HadarYisthak/MIPS-Based-MCU-Design/MCU Project/DUT/PLL.vhd

LIBRARY ieee;
USE ieee.std_logic_1164.all;

LIBRARY altera_mf;
USE altera_mf.all;

ENTITY PLL IS
	PORT
	(
		areset		: IN STD_LOGIC  := '0';
		inclk0		: IN STD_LOGIC  := '0';
		c0		: OUT STD_LOGIC ;
		locked		: OUT STD_LOGIC 
	);
END PLL;


ARCHITECTURE SYN OF pll IS

	SIGNAL sub_wire0	: STD_LOGIC ;
	SIGNAL sub_wire1	: STD_LOGIC_VECTOR (5 DOWNTO 0);
	SIGNAL sub_wire2	: STD_LOGIC ;
	SIGNAL sub_wire3	: STD_LOGIC ;
	SIGNAL sub_wire4	: STD_LOGIC_VECTOR (1 DOWNTO 0);
	SIGNAL sub_wire5_bv	: BIT_VECTOR (0 DOWNTO 0);
	SIGNAL sub_wire5	: STD_LOGIC_VECTOR (0 DOWNTO 0);



	COMPONENT altpll
	GENERIC (
		clk0_divide_by		: NATURAL;
		clk0_duty_cycle		: NATURAL;
		clk0_multiply_by	: NATURAL;
		clk0_phase_shift	: STRING;
		compensate_clock	: STRING;
		gate_lock_signal	: STRING;
		inclk0_input_frequency	: NATURAL;
		intended_device_family	: STRING;
		invalid_lock_multiplier	: NATURAL;
		lpm_hint		: STRING;
		lpm_type		: STRING;
		operation_mode		: STRING;
		port_activeclock	: STRING;
		port_areset		: STRING;
		port_clkbad0		: STRING;
		port_clkbad1		: STRING;
		port_clkloss		: STRING;
		port_clkswitch		: STRING;
		port_configupdate	: STRING;
		port_fbin		: STRING;
		port_inclk0		: STRING;
		port_inclk1		: STRING;
		port_locked		: STRING;
		port_pfdena		: STRING;
		port_phasecounterselect		: STRING;
		port_phasedone		: STRING;
		port_phasestep		: STRING;
		port_phaseupdown		: STRING;
		port_pllena		: STRING;
		port_scanaclr		: STRING;
		port_scanclk		: STRING;
		port_scanclkena		: STRING;
		port_scandata		: STRING;
		port_scandataout		: STRING;
		port_scandone		: STRING;
		port_scanread		: STRING;
		port_scanwrite		: STRING;
		port_clk0		: STRING;
		port_clk1		: STRING;
		port_clk2		: STRING;
		port_clk3		: STRING;
		port_clk4		: STRING;
		port_clk5		: STRING;
		port_clkena0		: STRING;
		port_clkena1		: STRING;
		port_clkena2		: STRING;
		port_clkena3		: STRING;
		port_clkena4		: STRING;
		port_clkena5		: STRING;
		port_extclk0		: STRING;
		port_extclk1		: STRING;
		port_extclk2		: STRING;
		port_extclk3		: STRING;
		valid_lock_multiplier		: NATURAL
	);
	PORT (
			areset	: IN STD_LOGIC ;
			clk	: OUT STD_LOGIC_VECTOR (5 DOWNTO 0);
			inclk	: IN STD_LOGIC_VECTOR (1 DOWNTO 0);
			locked	: OUT STD_LOGIC 
	);
	END COMPONENT;

BEGIN
	sub_wire5_bv(0 DOWNTO 0) <= "0";
	sub_wire5    <= To_stdlogicvector(sub_wire5_bv);
	locked    <= sub_wire0;
	sub_wire2    <= sub_wire1(0);
	c0    <= sub_wire2;
	sub_wire3    <= inclk0;
	sub_wire4    <= sub_wire5(0 DOWNTO 0) & sub_wire3;

	altpll_component : altpll
	GENERIC MAP (
		clk0_divide_by => 2,
		clk0_duty_cycle => 50,
		clk0_multiply_by => 1,
		clk0_phase_shift => "0",
		compensate_clock => "CLK0",
		gate_lock_signal => "NO",
		inclk0_input_frequency => 20000,
		intended_device_family => "Cyclone II",
		invalid_lock_multiplier => 5,
		lpm_hint => "CBX_MODULE_PREFIX=PLL",
		lpm_type => "altpll",
		operation_mode => "NORMAL",
		port_activeclock => "PORT_UNUSED",
		port_areset => "PORT_USED",
		port_clkbad0 => "PORT_UNUSED",
		port_clkbad1 => "PORT_UNUSED",
		port_clkloss => "PORT_UNUSED",
		port_clkswitch => "PORT_UNUSED",
		port_configupdate => "PORT_UNUSED",
		port_fbin => "PORT_UNUSED",
		port_inclk0 => "PORT_USED",
		port_inclk1 => "PORT_UNUSED",
		port_locked => "PORT_USED",
		port_pfdena => "PORT_UNUSED",
		port_phasecounterselect => "PORT_UNUSED",
		port_phasedone => "PORT_UNUSED",
		port_phasestep => "PORT_UNUSED",
		port_phaseupdown => "PORT_UNUSED",
		port_pllena => "PORT_UNUSED",
		port_scanaclr => "PORT_UNUSED",
		port_scanclk => "PORT_UNUSED",
		port_scanclkena => "PORT_UNUSED",
		port_scandata => "PORT_UNUSED",
		port_scandataout => "PORT_UNUSED",
		port_scandone => "PORT_UNUSED",
		port_scanread => "PORT_UNUSED",
		port_scanwrite => "PORT_UNUSED",
		port_clk0 => "PORT_USED",
		port_clk1 => "PORT_UNUSED",
		port_clk2 => "PORT_UNUSED",
		port_clk3 => "PORT_UNUSED",
		port_clk4 => "PORT_UNUSED",
		port_clk5 => "PORT_UNUSED",
		port_clkena0 => "PORT_UNUSED",
		port_clkena1 => "PORT_UNUSED",
		port_clkena2 => "PORT_UNUSED",
		port_clkena3 => "PORT_UNUSED",
		port_clkena4 => "PORT_UNUSED",
		port_clkena5 => "PORT_UNUSED",
		port_extclk0 => "PORT_UNUSED",
		port_extclk1 => "PORT_UNUSED",
		port_extclk2 => "PORT_UNUSED",
		port_extclk3 => "PORT_UNUSED",
		valid_lock_multiplier => 1
	)
	PORT MAP (
		areset => areset,
		inclk => sub_wire4,
		locked => sub_wire0,
		clk => sub_wire1
	);



END SYN;

-- ============================================================
-- CNX file retrieval info
-- ============================================================
-- Retrieval info: PRIVATE: ACTIVECLK_CHECK STRING "0"
-- Retrieval info: PRIVATE: BANDWIDTH STRING "1.000"
-- Retrieval info: PRIVATE: BANDWIDTH_FEATURE_ENABLED STRING "0"
-- Retrieval info: PRIVATE: BANDWIDTH_FREQ_UNIT STRING "MHz"
-- Retrieval info: PRIVATE: BANDWIDTH_PRESET STRING "Low"
-- Retrieval info: PRIVATE: BANDWIDTH_USE_AUTO STRING "1"
-- Retrieval info: PRIVATE: BANDWIDTH_USE_CUSTOM STRING "0"
-- Retrieval info: PRIVATE: BANDWIDTH_USE_PRESET STRING "0"
-- Retrieval info: PRIVATE: CLKBAD_SWITCHOVER_CHECK STRING "0"
-- Retrieval info: PRIVATE: CLKLOSS_CHECK STRING "0"
-- Retrieval info: PRIVATE: CLKSWITCH_CHECK STRING "1"
-- Retrieval info: PRIVATE: CNX_NO_COMPENSATE_RADIO STRING "0"
-- Retrieval info: PRIVATE: CREATE_CLKBAD_CHECK STRING "0"
-- Retrieval info: PRIVATE: CREATE_INCLK1_CHECK STRING "0"
-- Retrieval info: PRIVATE: CUR_DEDICATED_CLK STRING "c0"
-- Retrieval info: PRIVATE: CUR_FBIN_CLK STRING "c0"
-- Retrieval info: PRIVATE: DEVICE_SPEED_GRADE STRING "7"
-- Retrieval info: PRIVATE: DIV_FACTOR0 NUMERIC "2"
-- Retrieval info: PRIVATE: DUTY_CYCLE0 STRING "50.00000000"
-- Retrieval info: PRIVATE: EFF_OUTPUT_FREQ_VALUE0 STRING "75.000000"
-- Retrieval info: PRIVATE: EXPLICIT_SWITCHOVER_COUNTER STRING "0"
-- Retrieval info: PRIVATE: EXT_FEEDBACK_RADIO STRING "0"
-- Retrieval info: PRIVATE: GLOCKED_COUNTER_EDIT_CHANGED STRING "1"
-- Retrieval info: PRIVATE: GLOCKED_FEATURE_ENABLED STRING "1"
-- Retrieval info: PRIVATE: GLOCKED_MODE_CHECK STRING "0"
-- Retrieval info: PRIVATE: GLOCK_COUNTER_EDIT NUMERIC "1048575"
-- Retrieval info: PRIVATE: HAS_MANUAL_SWITCHOVER STRING "1"
-- Retrieval info: PRIVATE: INCLK0_FREQ_EDIT STRING "50.000"
-- Retrieval info: PRIVATE: INCLK0_FREQ_UNIT_COMBO STRING "MHz"
-- Retrieval info: PRIVATE: INCLK1_FREQ_EDIT STRING "100.000"
-- Retrieval info: PRIVATE: INCLK1_FREQ_EDIT_CHANGED STRING "1"
-- Retrieval info: PRIVATE: INCLK1_FREQ_UNIT_CHANGED STRING "1"
-- Retrieval info: PRIVATE: INCLK1_FREQ_UNIT_COMBO STRING "MHz"
-- Retrieval info: PRIVATE: INTENDED_DEVICE_FAMILY STRING "Cyclone II"
-- Retrieval info: PRIVATE: INT_FEEDBACK__MODE_RADIO STRING "1"
-- Retrieval info: PRIVATE: LOCKED_OUTPUT_CHECK STRING "1"
-- Retrieval info: PRIVATE: LONG_SCAN_RADIO STRING "1"
-- Retrieval info: PRIVATE: LVDS_MODE_DATA_RATE STRING "Not Available"
-- Retrieval info: PRIVATE: LVDS_MODE_DATA_RATE_DIRTY NUMERIC "0"
-- Retrieval info: PRIVATE: LVDS_PHASE_SHIFT_UNIT0 STRING "deg"
-- Retrieval info: PRIVATE: MIG_DEVICE_SPEED_GRADE STRING "Any"
-- Retrieval info: PRIVATE: MIRROR_CLK0 STRING "0"
-- Retrieval info: PRIVATE: MULT_FACTOR0 NUMERIC "3"
-- Retrieval info: PRIVATE: NORMAL_MODE_RADIO STRING "1"
-- Retrieval info: PRIVATE: OUTPUT_FREQ0 STRING "100.00000000"
-- Retrieval info: PRIVATE: OUTPUT_FREQ_MODE0 STRING "0"
-- Retrieval info: PRIVATE: OUTPUT_FREQ_UNIT0 STRING "MHz"
-- Retrieval info: PRIVATE: PHASE_RECONFIG_FEATURE_ENABLED STRING "0"
-- Retrieval info: PRIVATE: PHASE_RECONFIG_INPUTS_CHECK STRING "0"
-- Retrieval info: PRIVATE: PHASE_SHIFT0 STRING "0.00000000"
-- Retrieval info: PRIVATE: PHASE_SHIFT_STEP_ENABLED_CHECK STRING "0"
-- Retrieval info: PRIVATE: PHASE_SHIFT_UNIT0 STRING "deg"
-- Retrieval info: PRIVATE: PLL_ADVANCED_PARAM_CHECK STRING "0"
-- Retrieval info: PRIVATE: PLL_ARESET_CHECK STRING "1"
-- Retrieval info: PRIVATE: PLL_AUTOPLL_CHECK NUMERIC "1"
-- Retrieval info: PRIVATE: PLL_ENA_CHECK STRING "0"
-- Retrieval info: PRIVATE: PLL_ENHPLL_CHECK NUMERIC "0"
-- Retrieval info: PRIVATE: PLL_FASTPLL_CHECK NUMERIC "0"
-- Retrieval info: PRIVATE: PLL_FBMIMIC_CHECK STRING "0"
-- Retrieval info: PRIVATE: PLL_LVDS_PLL_CHECK NUMERIC "0"
-- Retrieval info: PRIVATE: PLL_PFDENA_CHECK STRING "0"
-- Retrieval info: PRIVATE: PLL_TARGET_HARCOPY_CHECK NUMERIC "0"
-- Retrieval info: PRIVATE: PRIMARY_CLK_COMBO STRING "inclk0"
-- Retrieval info: PRIVATE: RECONFIG_FILE STRING "PLL.mif"
-- Retrieval info: PRIVATE: SACN_INPUTS_CHECK STRING "0"
-- Retrieval info: PRIVATE: SCAN_FEATURE_ENABLED STRING "0"
-- Retrieval info: PRIVATE: SELF_RESET_LOCK_LOSS STRING "0"
-- Retrieval info: PRIVATE: SHORT_SCAN_RADIO STRING "0"
-- Retrieval info: PRIVATE: SPREAD_FEATURE_ENABLED STRING "0"
-- Retrieval info: PRIVATE: SPREAD_FREQ STRING "50.000"
-- Retrieval info: PRIVATE: SPREAD_FREQ_UNIT STRING "KHz"
-- Retrieval info: PRIVATE: SPREAD_PERCENT STRING "0.500"
-- Retrieval info: PRIVATE: SPREAD_USE STRING "0"
-- Retrieval info: PRIVATE: SRC_SYNCH_COMP_RADIO STRING "0"
-- Retrieval info: PRIVATE: STICKY_CLK0 STRING "1"
-- Retrieval info: PRIVATE: SWITCHOVER_COUNT_EDIT NUMERIC "1"
-- Retrieval info: PRIVATE: SWITCHOVER_FEATURE_ENABLED STRING "1"
-- Retrieval info: PRIVATE: SYNTH_WRAPPER_GEN_POSTFIX STRING "0"
-- Retrieval info: PRIVATE: USE_CLK0 STRING "1"
-- Retrieval info: PRIVATE: USE_CLKENA0 STRING "0"
-- Retrieval info: PRIVATE: USE_MIL_SPEED_GRADE NUMERIC "0"
-- Retrieval info: PRIVATE: ZERO_DELAY_RADIO STRING "0"
-- Retrieval info: LIBRARY: altera_mf altera_mf.altera_mf_components.all
-- Retrieval info: CONSTANT: CLK0_DIVIDE_BY NUMERIC "2"
-- Retrieval info: CONSTANT: CLK0_DUTY_CYCLE NUMERIC "50"
-- Retrieval info: CONSTANT: CLK0_MULTIPLY_BY NUMERIC "3"
-- Retrieval info: CONSTANT: CLK0_PHASE_SHIFT STRING "0"
-- Retrieval info: CONSTANT: COMPENSATE_CLOCK STRING "CLK0"
-- Retrieval info: CONSTANT: GATE_LOCK_SIGNAL STRING "NO"
-- Retrieval info: CONSTANT: INCLK0_INPUT_FREQUENCY NUMERIC "20000"
-- Retrieval info: CONSTANT: INTENDED_DEVICE_FAMILY STRING "Cyclone II"
-- Retrieval info: CONSTANT: INVALID_LOCK_MULTIPLIER NUMERIC "5"
-- Retrieval info: CONSTANT: LPM_TYPE STRING "altpll"
-- Retrieval info: CONSTANT: OPERATION_MODE STRING "NORMAL"
-- Retrieval info: CONSTANT: PORT_ACTIVECLOCK STRING "PORT_UNUSED"
-- Retrieval info: CONSTANT: PORT_ARESET STRING "PORT_USED"
-- Retrieval info: CONSTANT: PORT_CLKBAD0 STRING "PORT_UNUSED"
-- Retrieval info: CONSTANT: PORT_CLKBAD1 STRING "PORT_UNUSED"
-- Retrieval info: CONSTANT: PORT_CLKLOSS STRING "PORT_UNUSED"
-- Retrieval info: CONSTANT: PORT_CLKSWITCH STRING "PORT_UNUSED"
-- Retrieval info: CONSTANT: PORT_CONFIGUPDATE STRING "PORT_UNUSED"
-- Retrieval info: CONSTANT: PORT_FBIN STRING "PORT_UNUSED"
-- Retrieval info: CONSTANT: PORT_INCLK0 STRING "PORT_USED"
-- Retrieval info: CONSTANT: PORT_INCLK1 STRING "PORT_UNUSED"
-- Retrieval info: CONSTANT: PORT_LOCKED STRING "PORT_USED"
-- Retrieval info: CONSTANT: PORT_PFDENA STRING "PORT_UNUSED"
-- Retrieval info: CONSTANT: PORT_PHASECOUNTERSELECT STRING "PORT_UNUSED"
-- Retrieval info: CONSTANT: PORT_PHASEDONE STRING "PORT_UNUSED"
-- Retrieval info: CONSTANT: PORT_PHASESTEP STRING "PORT_UNUSED"
-- Retrieval info: CONSTANT: PORT_PHASEUPDOWN STRING "PORT_UNUSED"
-- Retrieval info: CONSTANT: PORT_PLLENA STRING "PORT_UNUSED"
-- Retrieval info: CONSTANT: PORT_SCANACLR STRING "PORT_UNUSED"
-- Retrieval info: CONSTANT: PORT_SCANCLK STRING "PORT_UNUSED"
-- Retrieval info: CONSTANT: PORT_SCANCLKENA STRING "PORT_UNUSED"
-- Retrieval info: CONSTANT: PORT_SCANDATA STRING "PORT_UNUSED"
-- Retrieval info: CONSTANT: PORT_SCANDATAOUT STRING "PORT_UNUSED"
-- Retrieval info: CONSTANT: PORT_SCANDONE STRING "PORT_UNUSED"
-- Retrieval info: CONSTANT: PORT_SCANREAD STRING "PORT_UNUSED"
-- Retrieval info: CONSTANT: PORT_SCANWRITE STRING "PORT_UNUSED"
-- Retrieval info: CONSTANT: PORT_clk0 STRING "PORT_USED"
-- Retrieval info: CONSTANT: PORT_clk1 STRING "PORT_UNUSED"
-- Retrieval info: CONSTANT: PORT_clk2 STRING "PORT_UNUSED"
-- Retrieval info: CONSTANT: PORT_clk3 STRING "PORT_UNUSED"
-- Retrieval info: CONSTANT: PORT_clk4 STRING "PORT_UNUSED"
-- Retrieval info: CONSTANT: PORT_clk5 STRING "PORT_UNUSED"
-- Retrieval info: CONSTANT: PORT_clkena0 STRING "PORT_UNUSED"
-- Retrieval info: CONSTANT: PORT_clkena1 STRING "PORT_UNUSED"
-- Retrieval info: CONSTANT: PORT_clkena2 STRING "PORT_UNUSED"
-- Retrieval info: CONSTANT: PORT_clkena3 STRING "PORT_UNUSED"
-- Retrieval info: CONSTANT: PORT_clkena4 STRING "PORT_UNUSED"
-- Retrieval info: CONSTANT: PORT_clkena5 STRING "PORT_UNUSED"
-- Retrieval info: CONSTANT: PORT_extclk0 STRING "PORT_UNUSED"
-- Retrieval info: CONSTANT: PORT_extclk1 STRING "PORT_UNUSED"
-- Retrieval info: CONSTANT: PORT_extclk2 STRING "PORT_UNUSED"
-- Retrieval info: CONSTANT: PORT_extclk3 STRING "PORT_UNUSED"
-- Retrieval info: CONSTANT: VALID_LOCK_MULTIPLIER NUMERIC "1"
-- Retrieval info: USED_PORT: @clk 0 0 6 0 OUTPUT_CLK_EXT VCC "@clk[5..0]"
-- Retrieval info: USED_PORT: @extclk 0 0 4 0 OUTPUT_CLK_EXT VCC "@extclk[3..0]"
-- Retrieval info: USED_PORT: @inclk 0 0 2 0 INPUT_CLK_EXT VCC "@inclk[1..0]"
-- Retrieval info: USED_PORT: areset 0 0 0 0 INPUT GND "areset"
-- Retrieval info: USED_PORT: c0 0 0 0 0 OUTPUT_CLK_EXT VCC "c0"
-- Retrieval info: USED_PORT: inclk0 0 0 0 0 INPUT_CLK_EXT GND "inclk0"
-- Retrieval info: USED_PORT: locked 0 0 0 0 OUTPUT GND "locked"
-- Retrieval info: CONNECT: @areset 0 0 0 0 areset 0 0 0 0
-- Retrieval info: CONNECT: @inclk 0 0 1 1 GND 0 0 0 0
-- Retrieval info: CONNECT: @inclk 0 0 1 0 inclk0 0 0 0 0
-- Retrieval info: CONNECT: c0 0 0 0 0 @clk 0 0 1 0
-- Retrieval info: CONNECT: locked 0 0 0 0 @locked 0 0 0 0
-- Retrieval info: GEN_FILE: TYPE_NORMAL PLL.vhd TRUE
-- Retrieval info: GEN_FILE: TYPE_NORMAL PLL.ppf TRUE
-- Retrieval info: GEN_FILE: TYPE_NORMAL PLL.inc FALSE
-- Retrieval info: GEN_FILE: TYPE_NORMAL PLL.cmp TRUE
-- Retrieval info: GEN_FILE: TYPE_NORMAL PLL.bsf FALSE
-- Retrieval info: GEN_FILE: TYPE_NORMAL PLL_inst.vhd FALSE
-- Retrieval info: LIB_FILE: altera_mf
-- Retrieval info: CBX_MODULE_PREFIX: ON
