HadarYisthak/MIPS-Based-MCU-Design/MCU Project/DUT/IDECODE.VHD

---------------------------------------------------------------------------------------------
-- Copyright 2025 Hananya Ribo 
-- Advanced CPU architecture and Hardware Accelerators Lab 361-1-4693 BGU
---------------------------------------------------------------------------------------------
--  Idecode module (implements the register file for the MIPS computer
LIBRARY IEEE; 		
USE IEEE.STD_LOGIC_1164.ALL;
USE IEEE.STD_LOGIC_ARITH.ALL;
USE IEEE.STD_LOGIC_UNSIGNED.ALL;


ENTITY Idecode IS
	generic(
		DATA_BUS_WIDTH : integer := 32
	);
	PORT(		clk_i,rst_i	: IN 	STD_LOGIC;
			instruction_i 	: IN 	STD_LOGIC_VECTOR(DATA_BUS_WIDTH-1 DOWNTO 0);
			dtcm_data_rd_i 	: IN 	STD_LOGIC_VECTOR(DATA_BUS_WIDTH-1 DOWNTO 0);
			alu_result_i	: IN 	STD_LOGIC_VECTOR(DATA_BUS_WIDTH-1 DOWNTO 0);
			RegWrite_ctrl_i : IN 	STD_LOGIC;
			MemtoReg_ctrl_i : IN 	STD_LOGIC;
			RegDst_ctrl_i 	: IN 	STD_LOGIC;
			jal_i		: IN	STD_LOGIC;
			pc_plus4_i	: IN	STD_LOGIC_VECTOR(9 DOWNTO 0);
			pc_intr		: IN 	STD_LOGIC_VECTOR(9 DOWNTO 0);
			Read_ISR_PC	: IN 	STD_LOGIC;
			INTR		: IN 	STD_LOGIC;
			JUMP		: IN 	STD_LOGIC;
			GIE		: OUT	STD_LOGIC;
			read_data1_o	: OUT 	STD_LOGIC_VECTOR(DATA_BUS_WIDTH-1 DOWNTO 0);
			read_data2_o	: OUT 	STD_LOGIC_VECTOR(DATA_BUS_WIDTH-1 DOWNTO 0);
			sign_extend_o 	: OUT 	STD_LOGIC_VECTOR(DATA_BUS_WIDTH-1 DOWNTO 0);
			shamt		: OUT	STD_LOGIC_VECTOR(4 DOWNTO 0)		 
	);
END Idecode;


ARCHITECTURE behavior OF Idecode IS
TYPE register_file IS ARRAY (0 TO 31) OF STD_LOGIC_VECTOR(DATA_BUS_WIDTH-1 DOWNTO 0);

	SIGNAL RF_q			: register_file;
	SIGNAL write_reg_addr_w 	: STD_LOGIC_VECTOR( 4 DOWNTO 0 );
	SIGNAL write_reg_data_w		: STD_LOGIC_VECTOR( 31 DOWNTO 0 );
	SIGNAL rs_register_w		: STD_LOGIC_VECTOR( 4 DOWNTO 0 );
	SIGNAL rt_register_w		: STD_LOGIC_VECTOR( 4 DOWNTO 0 );
	SIGNAL rd_register_w		: STD_LOGIC_VECTOR( 4 DOWNTO 0 );
	SIGNAL imm_value_w		: STD_LOGIC_VECTOR( 15 DOWNTO 0 );

BEGIN
-------????? ???? ???????
	rs_register_w 			<= instruction_i(25 DOWNTO 21);
   	rt_register_w 			<= instruction_i(20 DOWNTO 16);
   	rd_register_w			<= "11111" WHEN jal_i ='1' ELSE instruction_i(15 DOWNTO 11);
   	imm_value_w 			<= instruction_i(15 DOWNTO 0);
	shamt				<= instruction_i(10 DOWNTO 6);
	
	-- Read Register 1 Operation 
	read_data1_o <= RF_q(CONV_INTEGER(rs_register_w));
	
	-- Read Register 2 Operation		 
	read_data2_o <= RF_q(CONV_INTEGER(rt_register_w));
	
	-- Mux for Register Write Address
	write_reg_addr_w <= rd_register_w WHEN RegDst_ctrl_i = '1' ELSE 
						rt_register_w;
	
	-- Mux to bypass data memory for Rformat instructions ???? ????
	write_reg_data_w <= 	alu_result_i(DATA_BUS_WIDTH-1 DOWNTO 0) WHEN (MemtoReg_ctrl_i = '0' and jal_i='0') ELSE
				"0000000000000000000000" & pc_plus4_i(9 DOWNTO 0) WHEN jal_i ='1' ELSE
				dtcm_data_rd_i;
	
	-- Sign Extend 16-bits to 32-bits
    	sign_extend_o <= 	X"0000" & imm_value_w WHEN imm_value_w(15) = '0' ELSE
						X"FFFF" & imm_value_w;

------------ Global interrupt enable GIE ------------------------
	GIE				<= RF_q(26)(0);

-----------------------------GIE - GLOBAL BIT INTERRUPT, ENABLE INTERRUPT EHWN 1
process(clk_i, rst_i)
begin
    if rst_i='1' then
        -- Reset all registers
        for i in 0 to 31 loop
            RF_q(i) <=  CONV_STD_LOGIC_VECTOR(0,32);
        end loop;
    elsif (clk_i'event and clk_i='1') then
        -- Regular write
        if RegWrite_ctrl_i='1' and write_reg_addr_w /= 0 then
            RF_q(CONV_INTEGER(write_reg_addr_w)) <= write_reg_data_w;
        end if;

        -- $k0 GIE handling
        if INTR='1' then
            RF_q(26)(0) <= '0';  -- disable interrupts
        elsif rs_register_w="11011" and Jump='1' then
            RF_q(26)(0) <= '1';  -- enable interrupts
        end if;

        -- $k1 EPC handling
        if Read_ISR_PC='1' then
            RF_q(27) <=  X"00000"& "00" & pc_intr; 
        end if;
    end if;
end process;




END behavior;
