HadarYisthak/MIPS-Based-MCU-Design/MCU Project/DUT/OutPeripheral.vhd

--------------- Output Peripheral Module 
LIBRARY IEEE;
USE IEEE.STD_LOGIC_1164.ALL;
USE IEEE.STD_LOGIC_ARITH.ALL;
USE work.aux_package.ALL;
-------------- ENTITY --------------------
ENTITY OutputPeripheral IS
	GENERIC (SevenSeg	: BOOLEAN := TRUE;
		 IOSize		: INTEGER := 7); -- 7 WHEN HEX, 8 WHEN LEDs
	PORT( 
		MemRead		: IN	STD_LOGIC;
		clock		: IN 	STD_LOGIC;
		reset		: IN 	STD_LOGIC;
		MemWrite	: IN	STD_LOGIC;
		ChipSelect	: IN 	STD_LOGIC;
		Data		: INOUT	STD_LOGIC_VECTOR(7 DOWNTO 0);
		GPOutput	: OUT	STD_LOGIC_VECTOR(IOSize-1 DOWNTO 0)
		);
END OutputPeripheral;
------------ ARCHITECTURE ----------------
ARCHITECTURE structure OF OutputPeripheral IS
	SIGNAL Latch_o	: STD_LOGIC_VECTOR(7 DOWNTO 0);
BEGIN
	--- Added to test unaffected by michael 23:16
	
	PROCESS(clock)
	BEGIN
	IF (reset = '1') THEN
		Latch_o	<= X"00";
	ELSIF (falling_edge(clock)) THEN
		IF (MemWrite = '1' AND ChipSelect = '1') THEN
			Latch_o <= Data;
		END IF;
	END IF;
	END PROCESS;
	-----------------------------------------------------------------------------------------

	Data	<= Latch_o WHEN (MemRead = '1' AND ChipSelect = '1') 	ELSE (others => 'Z'); 

SEG: 	IF (SevenSeg = TRUE) GENERATE SevenSegDec: SevenSegDecoder
							PORT MAP(data	=> Latch_o(3 DOWNTO 0),
							 	seg	=> GPOutput);
							END GENERATE SEG;
	
	NO_SEG:
		IF (SevenSeg = FALSE) GENERATE
			GPOutput <= Latch_o;
		END GENERATE NO_SEG;
	
END structure;
